rupeeangad-rutech/ServoTurret-ESP32/schematic/AutonomousObstacleAvoidingServoTurret.kicad_sch

## KiCad design schematic/AutonomousObstacleAvoidingServoTurret.kicad_sch (2026-06-30)

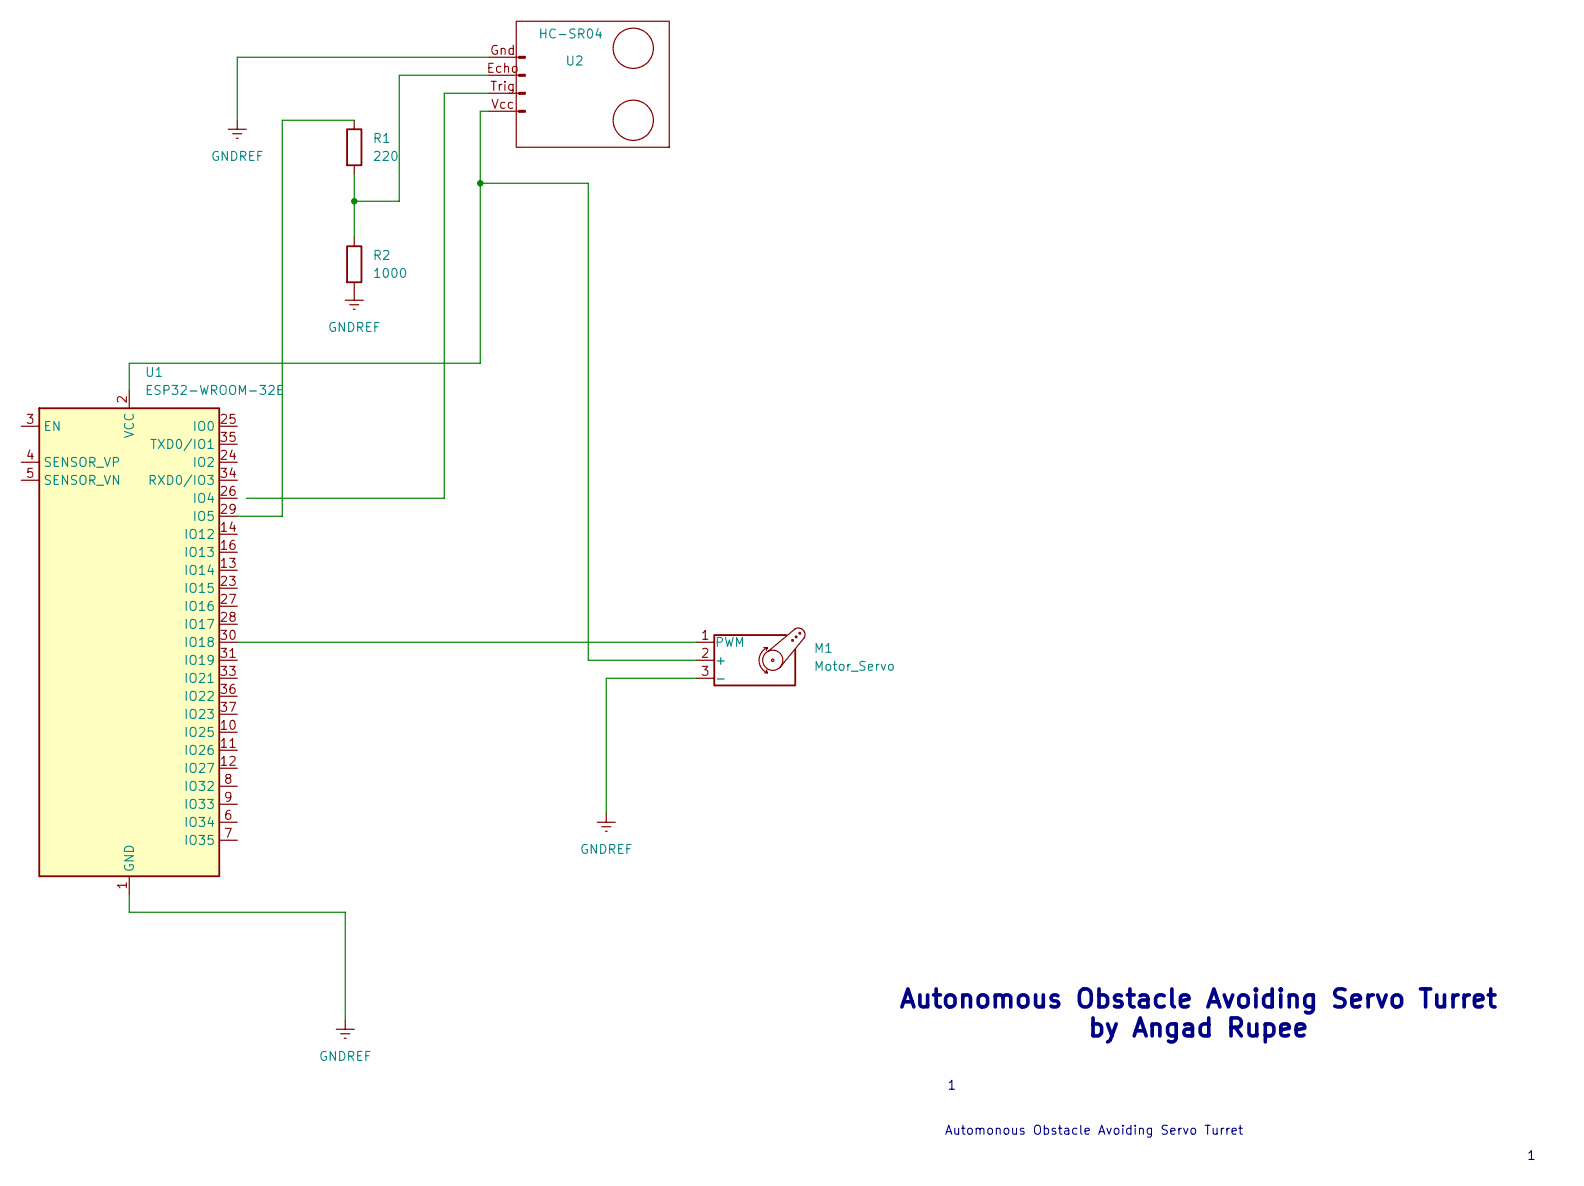
[picture p4: schematic AutonomousObstacleAvoidingServoTurret.kicad_sch]

Parts:
M1: Motor_Servo
R1: 220
R2: 1000
U1: ESP32-WROOM-32E; ESP32-WROOM-32D
U2: HC-SR04

Connections:
GNDREF: M1.3 (-), R2.2, U1.1 (GND), U1.15 (GND), U1.38 (GND), U1.39 (GND), U2.Gnd (Pin_4)
unnamed: M1.1 (PWM), U1.30 (IO18)
unnamed: M1.2 (+), U1.2 (VCC), U2.Vcc (Pin_1)
unnamed: R1.1, U1.29 (IO5)
unnamed: R1.2, R2.1, U2.Echo (Pin_3)

Notes on the sheet:
Automonous Obstacle Avoiding Servo Turret
Autonomous Obstacle Avoiding Servo Turret by Angad Rupee
